MajicDesigns/APM_Clock/media/photo/APM_Clock_BoostConverter.png

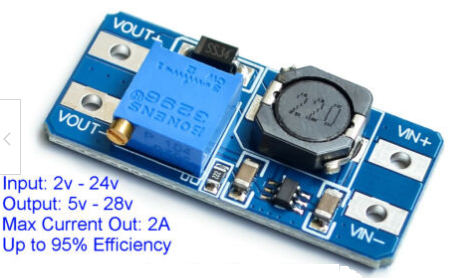
media/photo/APM_Clock_BoostConverter.png
