MajicDesigns/APM_Clock/media/photo/APM_Clock_Case2.JPG

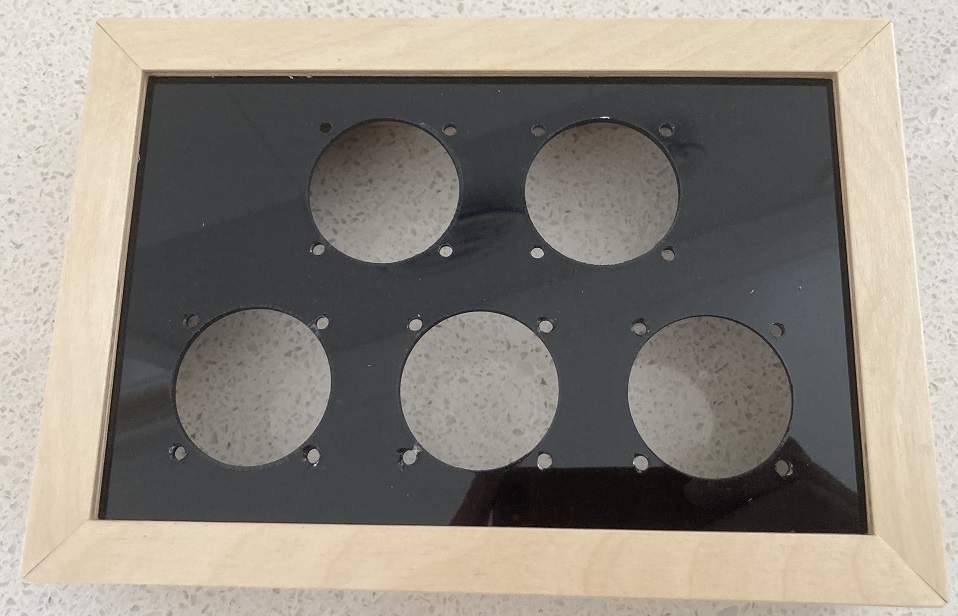
media/photo/APM_Clock_Case2.JPG
