MajicDesigns/APM_Clock/media/photo/APM_Clock_Case3.JPG

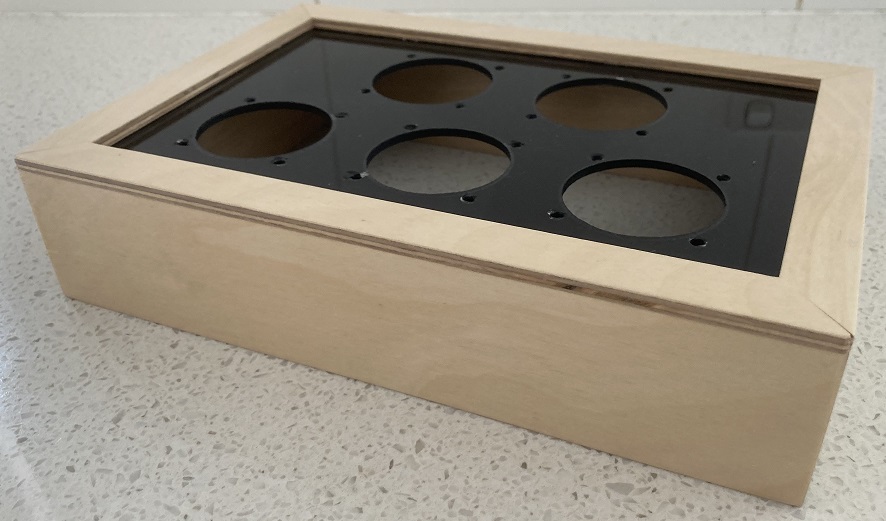
media/photo/APM_Clock_Case3.JPG
