MajicDesigns/APM_Clock/media/photo/APM_Clock_Connector.JPG

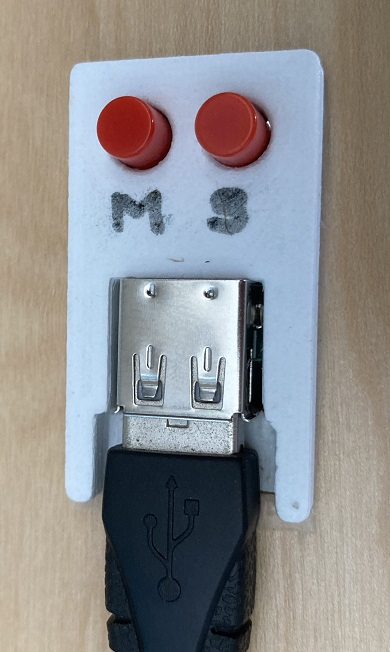
media/photo/APM_Clock_Connector.JPG
