MajicDesigns/APM_Clock/media/photo/APM_Clock_Final1.JPG

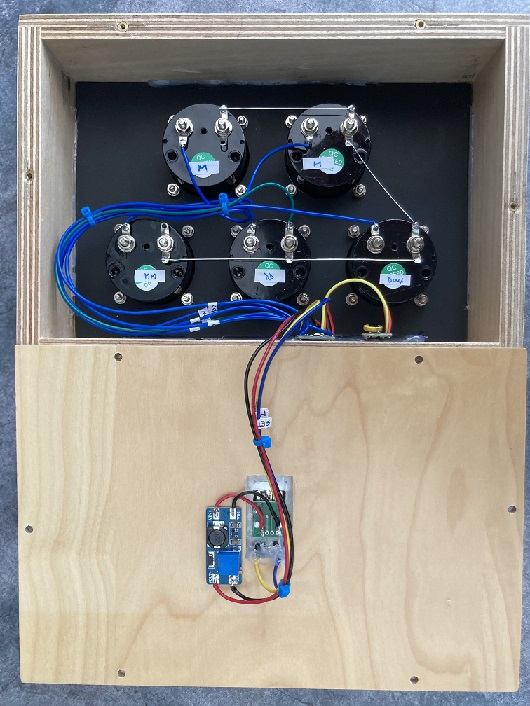
media/photo/APM_Clock_Final1.JPG
