MajicDesigns/APM_Clock/media/photo/APM_clock_Final2.JPG

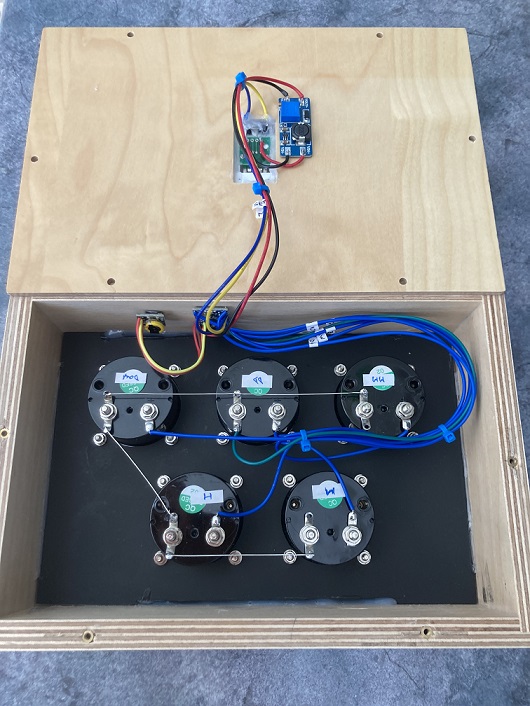
media/photo/APM_clock_Final2.JPG
