MajicDesigns/APM_Clock/media/photo/APM_Clock_NewFaceplates.png

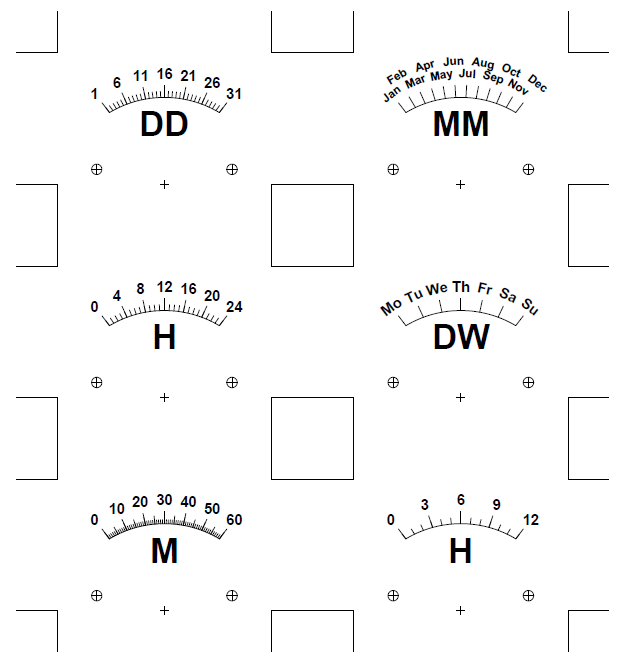
media/photo/APM_Clock_NewFaceplates.png
