MajicDesigns/APM_Clock/media/photo/APM_Clock_OriginalFaceplate.jpg

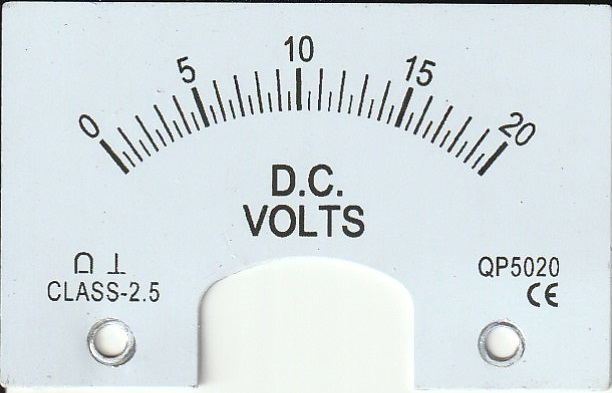
media/photo/APM_Clock_OriginalFaceplate.jpg
