MajicDesigns/APM_Clock/media/photo/APM_Clock_Panel_Meter.jpg

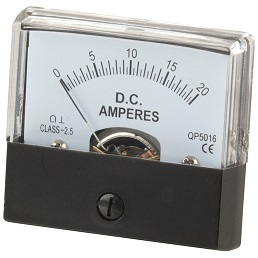
media/photo/APM_Clock_Panel_Meter.jpg
