MajicDesigns/APM_Clock/media/photo/APM_Clock_Plate_Model.png

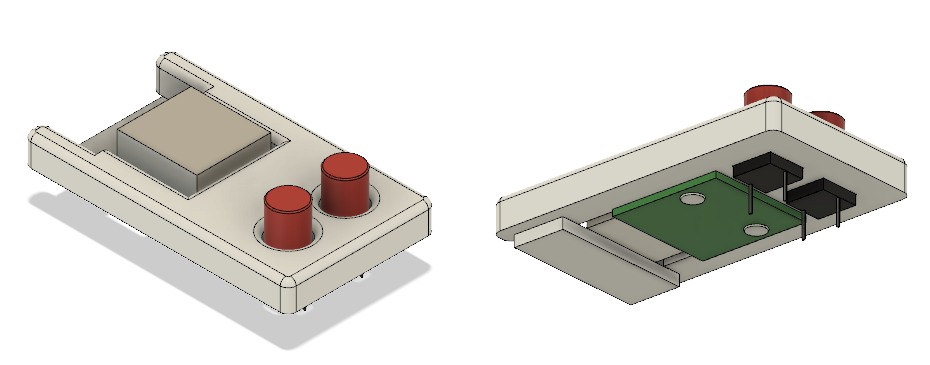
media/photo/APM_Clock_Plate_Model.png
