MajicDesigns/APM_Clock/media/photo/APM_Clock_Prototype.JPG

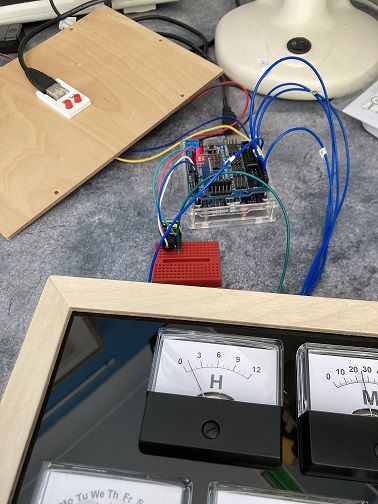
media/photo/APM_Clock_Prototype.JPG
