MajicDesigns/APM_Clock/media/photo/APM_Clock_RTC_Module.jpg

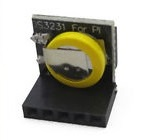
media/photo/APM_Clock_RTC_Module.jpg
