MajicDesigns/APM_Clock/media/photo/APM_Clock_System.png

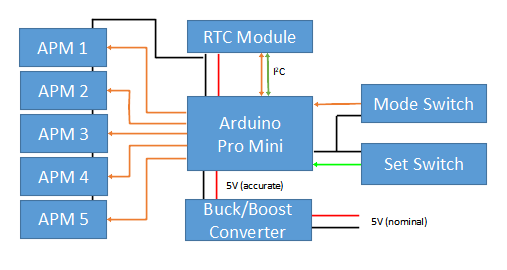
media/photo/APM_Clock_System.png
