MajicDesigns/APM_Clock/media/photo/APM_Clock_TactSwitch.png

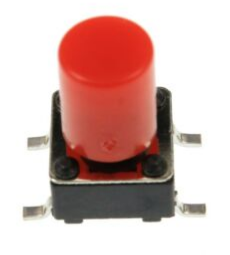
media/photo/APM_Clock_TactSwitch.png
